SzanderB/BubbleHockeyScoreboard/Pictures/IMG_0029.JPEG

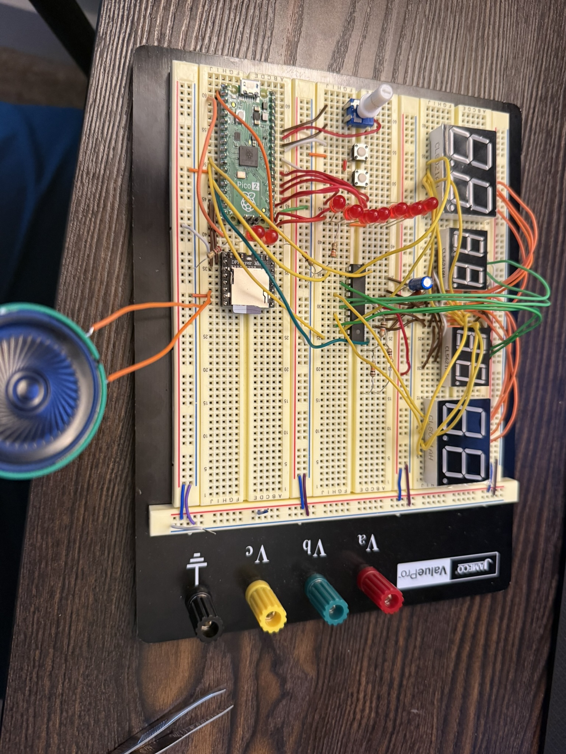
Pictures/IMG_0029.JPEG
