SzanderB/BubbleHockeyScoreboard/Pictures/IMG_0110.JPEG

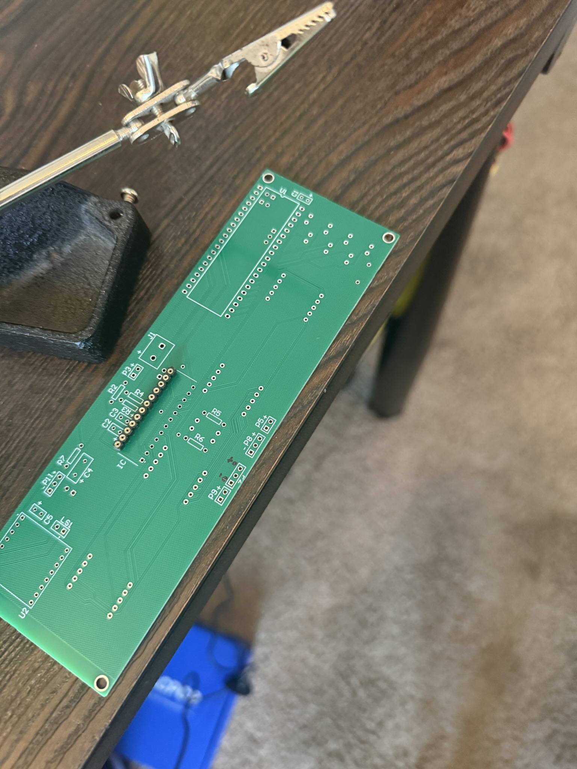
Pictures/IMG_0110.JPEG
