SzanderB/BubbleHockeyScoreboard/Pictures/IMG_0139.JPEG

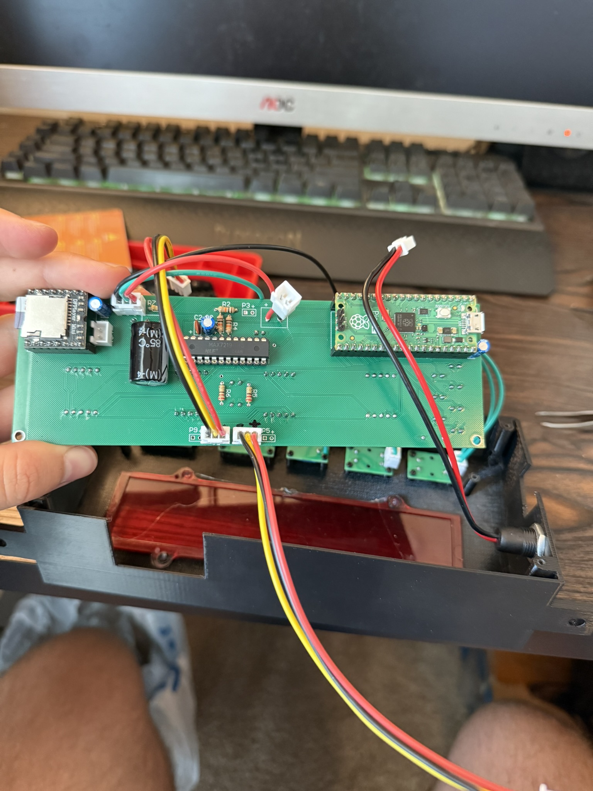
Pictures/IMG_0139.JPEG
